sawaiz/sakuraPlanter/docs/assets/hero.jpg

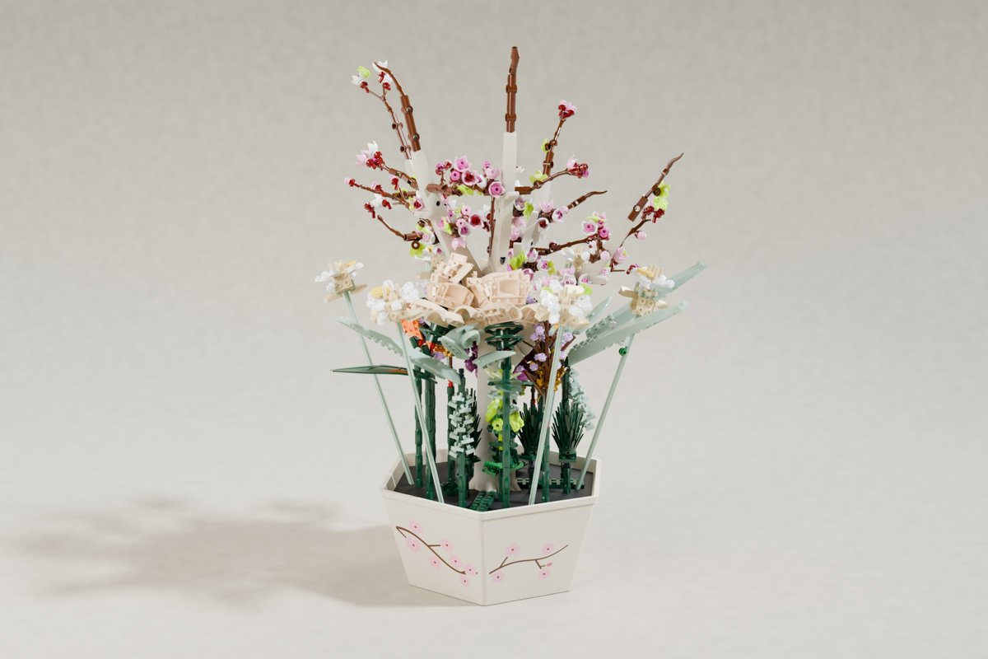
docs/assets/hero.jpg
