sawaiz/sakuraPlanter/print/plates/08_soil-mat.3mf

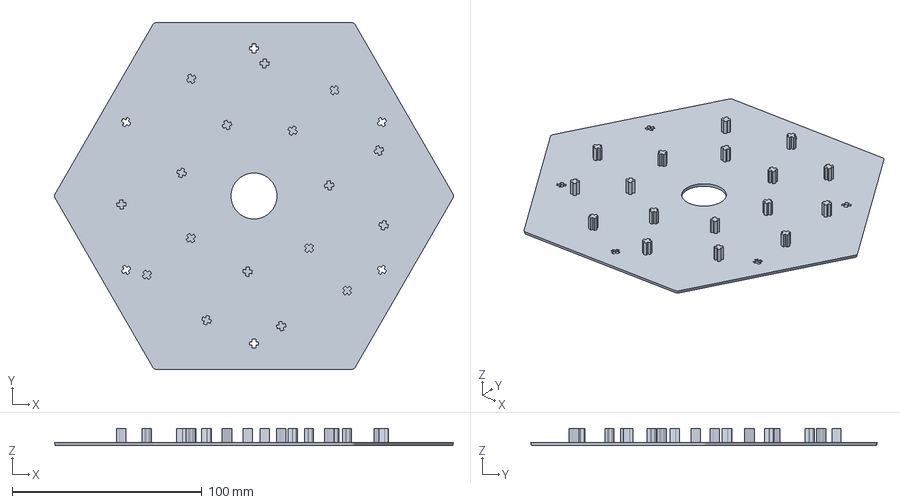
[picture p45: CAD file, 2026-10-06]
print/plates/08_soil-mat.3mf
210.2 x 182.6 x 9.10 mm
