sawaiz/sakuraPlanter/cad/out/Foot.step

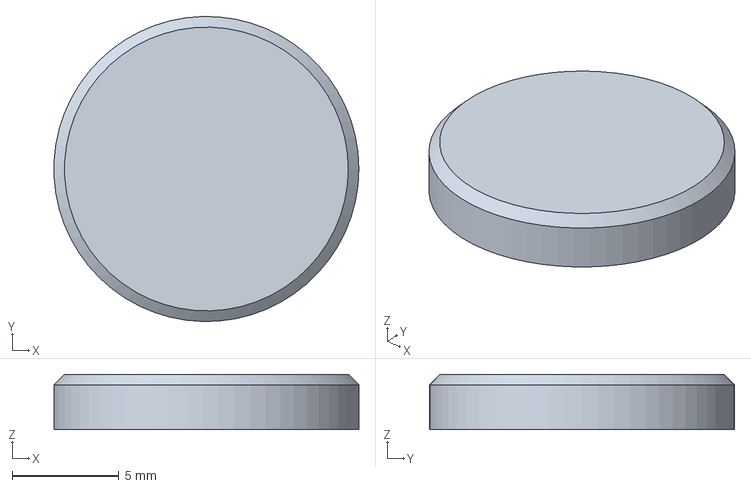
[picture p46: CAD file, 2026-10-06]
cad/out/Foot.step
14.3 x 14.3 x 2.60 mm
