sawaiz/sakuraPlanter/print/plates/06_branches.3mf

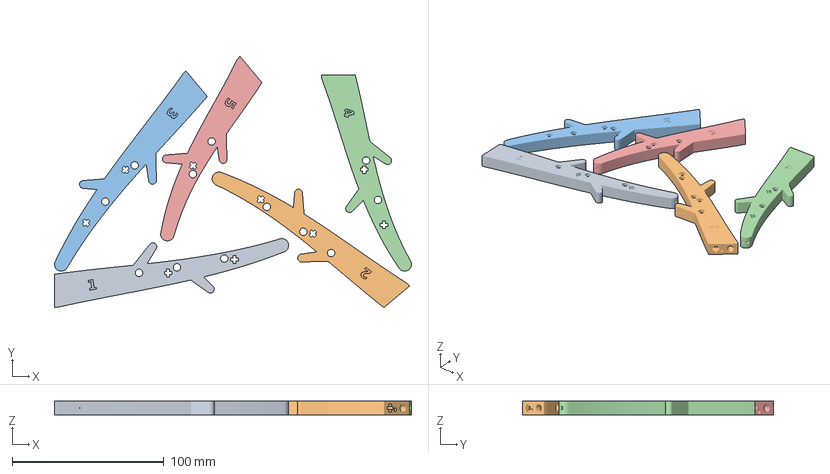
[picture p47: CAD file, 2026-10-06]
print/plates/06_branches.3mf
235.5 x 165.7 x 9.00 mm
Branch1 1
Branch2 2
Branch3 3
Branch4 4
Branch5 5
