sawaiz/sakuraPlanter/cad/out/FT4_StubFace.step

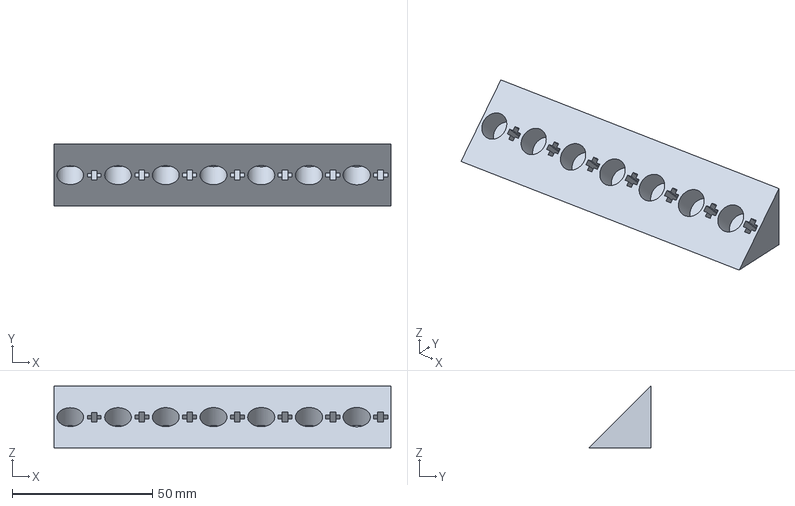
[picture p48: CAD file, 2026-10-06]
cad/out/FT4_StubFace.step
120.0 x 22.0 x 22.0 mm
