sawaiz/sakuraPlanter/print/plates/01_fit-kit-pla.3mf

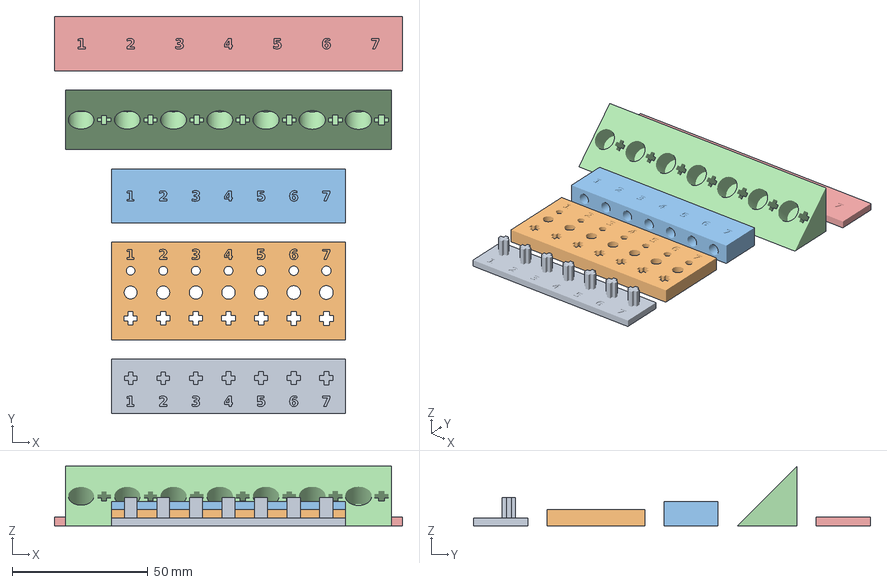
[picture p49: CAD file, 2026-10-06]
print/plates/01_fit-kit-pla.3mf
128.0 x 146.0 x 22.0 mm
FT1_FloorPegs 1
FT2_VerticalHoles 2
FT3_BranchRoot 3
FT4_StubFace 4
FT5_FootPockets 5
