sawaiz/sakuraPlanter/cad/out/Trunk.step

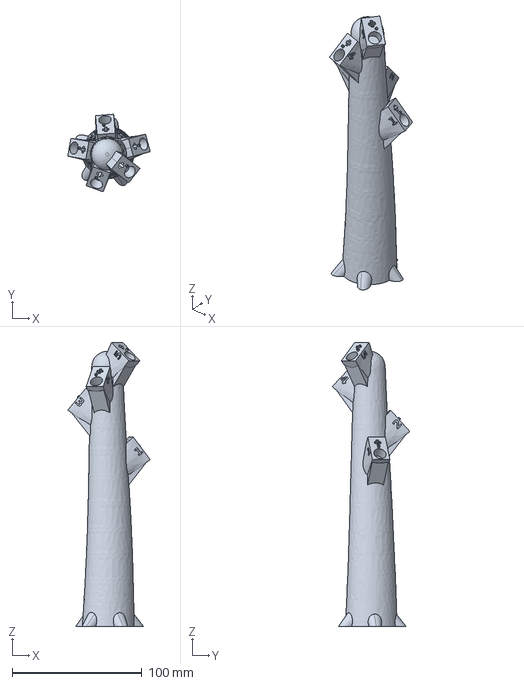
[picture p50: CAD file, 2026-10-06]
cad/out/Trunk.step
63.6 x 59.9 x 218.8 mm
