sawaiz/sakuraPlanter/print/stl/Branch2.stl

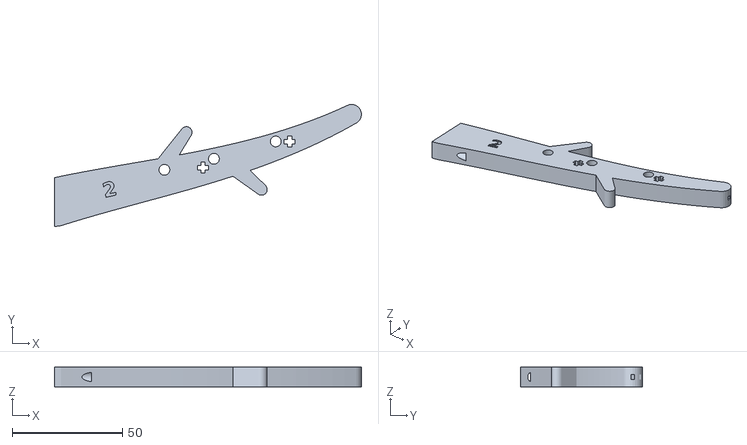
[picture p51: CAD file, 2026-10-06]
print/stl/Branch2.stl
139.5 x 55.5 x 9.00
