sawaiz/sakuraPlanter/cad/out/FT1_FloorPegs.step

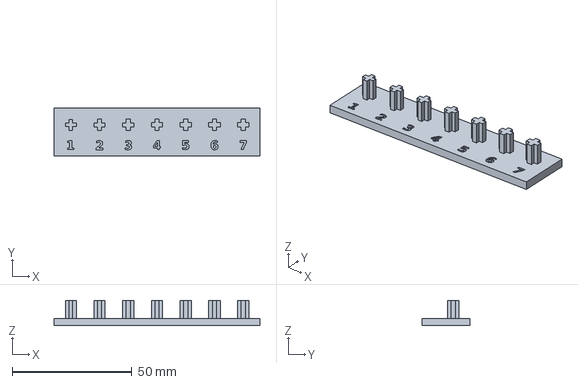
[picture p52: CAD file, 2026-10-06]
cad/out/FT1_FloorPegs.step
86.0 x 20.0 x 10.5 mm
