sawaiz/sakuraPlanter/cad/out/FT5_FootPockets.step

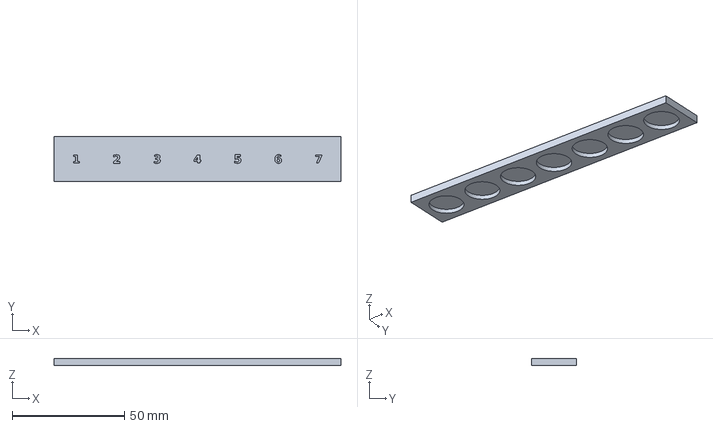
[picture p53: CAD file, 2026-10-06]
cad/out/FT5_FootPockets.step
128.0 x 20.0 x 3.20 mm
